EECS-NTNU/lynsyn-firmware/mcu/common/swo.c

/******************************************************************************
 *
 *  This file is part of the Lynsyn PMU firmware.
 *
 *  Copyright 2018-2019 Asbjørn Djupdal, NTNU
 *
 *****************************************************************************/

#include <stdarg.h>
#include <stdio.h>

#include <em_device.h>
#include <em_cmu.h>
#include <em_gpio.h>
#include <em_i2c.h>
#include <em_system.h>
#include <em_chip.h>

/* *** This is a Serial Wire Output based console.*** */
/* To use it you must do two things: */
/* 1. Set up the Serial Wire Output in your application. */
/*    You can use the function below for this. */
/*    NOTE: This funtion is different than the one used */
/*    in the profiler! */
/* 2. To print a single character use the CMSIS function */
/*    ITM_SendChar(char c). */

void swoInit(void) {
  /* Enable GPIO clock. */
  CMU->HFPERCLKEN0 |= CMU_HFPERCLKEN0_GPIO;

  /* Enable Serial wire output pin */
  GPIO->ROUTE |= GPIO_ROUTE_SWOPEN;

  /* Set location 0 */
  GPIO->ROUTE = (GPIO->ROUTE & ~(_GPIO_ROUTE_SWLOCATION_MASK)) | GPIO_ROUTE_SWLOCATION_LOC0;

  /* Enable output on pin - GPIO Port F, Pin 2 */
  GPIO->P[5].MODEL &= ~(_GPIO_P_MODEL_MODE2_MASK);
  GPIO->P[5].MODEL |= GPIO_P_MODEL_MODE2_PUSHPULL;

  /* Enable debug clock AUXHFRCO */
  CMU->OSCENCMD = CMU_OSCENCMD_AUXHFRCOEN;

  /* Wait until clock is ready */
  while (!(CMU->STATUS & CMU_STATUS_AUXHFRCORDY));

  /* Enable trace in core debug */
  CoreDebug->DEMCR |= CoreDebug_DEMCR_TRCENA_Msk;
  ITM->LAR  = 0xC5ACCE55;
  ITM->TER  = 0x0;
  ITM->TCR  = 0x0;
  TPI->SPPR = 2;
  TPI->ACPR = 0xf;
  ITM->TPR  = 0x0;
  DWT->CTRL = 0x400003FE;
  ITM->TCR  = 0x0001000D;
  TPI->FFCR = 0x00000100;
  ITM->TER  = 0x1;
}
