EECS-NTNU/lynsyn-firmware/mcu/main/zynq.h

/******************************************************************************
 *
 *  This file is part of the Lynsyn PMU firmware.
 *
 *  Copyright 2018-2019 Asbjørn Djupdal, NTNU
 *
 *****************************************************************************/

#ifndef ZYNQ_H
#define ZYNQ_H

#define PS_TAP_IDCODE 0x28e20126

#define JTAG_CTRL_ARM_DAP 2
#define JTAG_CTRL_PL_TAP  1

#define PS_JTAG_CTRL 0x824

#endif
